PSGXerus/PK6/hw/spice/power.asc

C1: EuropeanPolcap; 100µ; V=10 Irms=3.87298 Rser=0.015 Lser=0
C2: cap; 470µ
D1: diode
D2: diode
D3: diode
D5: LED
L1: ind; 100n
M1: nmos; IRLHS6376
Q1: npn; BC547B
Q2: npn; BC517
R1: EuropeanResistor; 4.7k
R2: EuropeanResistor; 100k
R3: EuropeanResistor; 100k
R4: EuropeanResistor; 470k
R5: EuropeanResistor; 1k
R6: EuropeanResistor; 1k
R7: EuropeanResistor; 50
R8: EuropeanResistor; 120
R9: EuropeanResistor; 10k
R10: EuropeanResistor; 10k
reset: voltage; PWL(0 1 0.5 0)
S1: sw
S2: sw; RELAIS
S3: sw
V1: voltage; 5
V2: voltage; PWL(0 0 2.5 0 2.5001 3.3 11.5 3.3 11.5001 0)
voltage_test: voltage; PWL(0 0 1 0 1.001 1 1.5 1 1.5001 0 10 0 10.001 1 10.5 1 10.5001 0 15 0)
Named nets: 0, Switch_on, Vpi, gnd_relais, v_from_pi, v_from_switch
.tran 0 100 0
.model SW SW(Ron=1m Roff=1meg Vt=0.5 Vh=0)
.model RELAIS SW(Ron=1m Roff=1meg Vt=2.125 Vh=1,625)
.model BC517 NPN( BF=30K BR=1 IS= 3.02200000000000E-0026 RB=10 RC=0  CJC=97.92P VJC=750M MJC=330M TR=10N CJE=201.2P VJE=750M MJE=330M TF=357.1P EG=1.11 VAF=100  XTB=2M KF=0 AF=1 )
